karnxx/bonbon/images/Screenshot 2026-04-02 172829.png

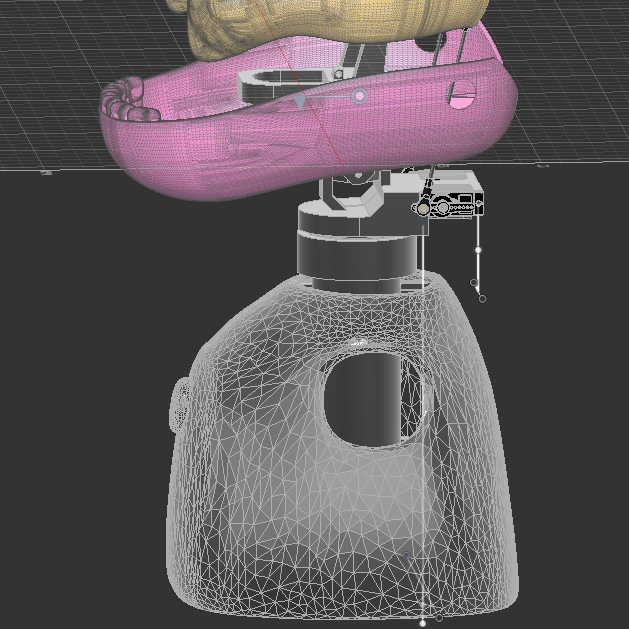
images/Screenshot 2026-04-02 172829.png
