karnxx/bonbon/cad/printed parts/stls/1xbothhands.stl

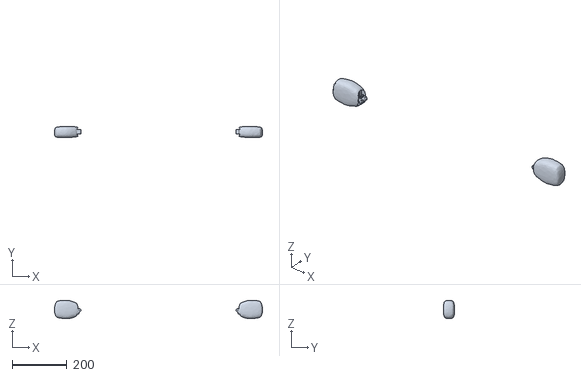
[picture p11: CAD file, 2026-04-18]
cad/printed parts/stls/1xbothhands.stl
756.6 x 40.9 x 67.3
