karnxx/bonbon/cad/printed parts/stls/1xuplidcontroller.stl

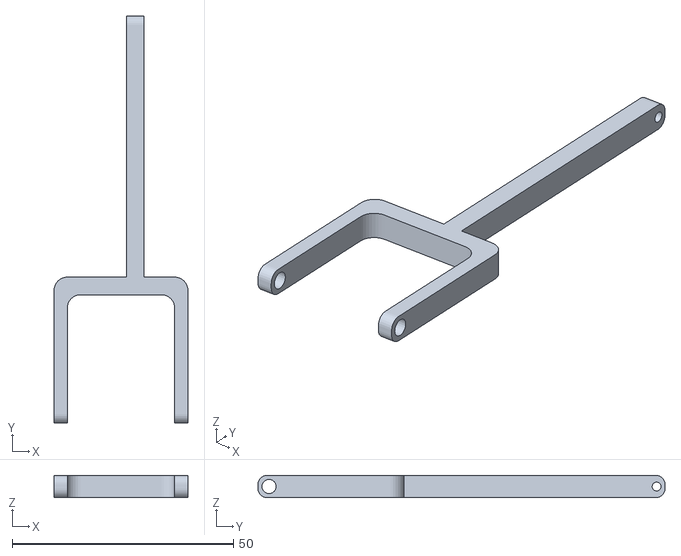
[picture p12: CAD file, 2026-04-18]
cad/printed parts/stls/1xuplidcontroller.stl
30.3 x 92.0 x 5.00
