karnxx/bonbon/cad/printed parts/stls/1xsnoutl.stl

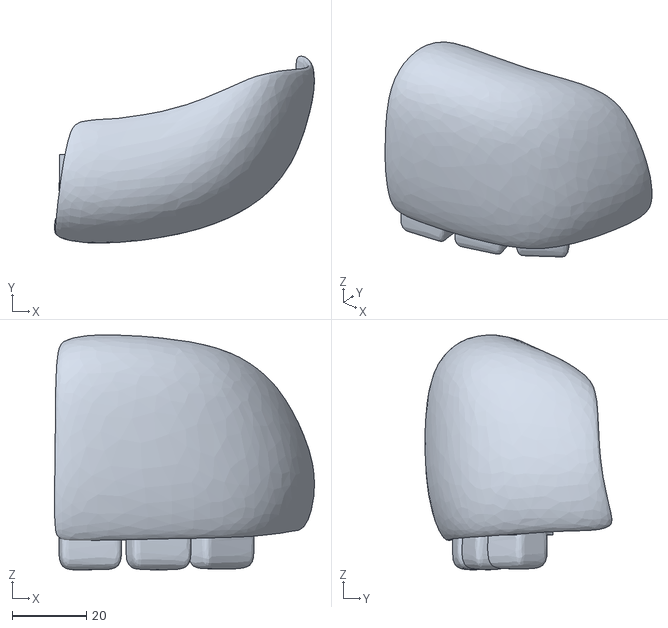
[picture p13: CAD file, 2026-04-18]
cad/printed parts/stls/1xsnoutl.stl
70.2 x 50.5 x 63.5
