karnxx/bonbon/cad/printed parts/stls/2xuptilt.stl

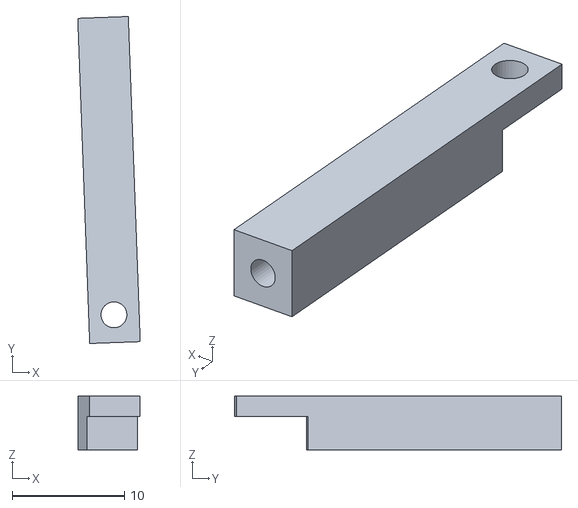
[picture p14: CAD file, 2026-04-18]
cad/printed parts/stls/2xuptilt.stl
5.56 x 29.1 x 4.80
