karnxx/bonbon/cad/printed parts/stls/1xjawshaft.stl

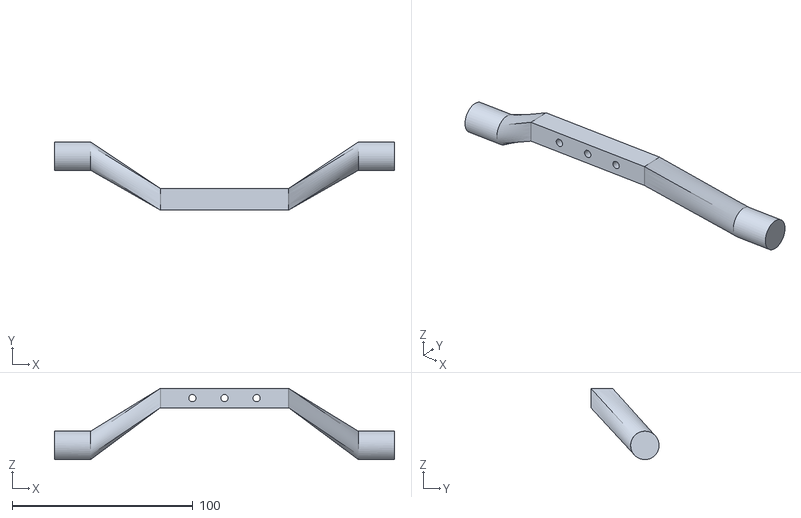
[picture p15: CAD file, 2026-04-18]
cad/printed parts/stls/1xjawshaft.stl
188.0 x 37.7 x 39.4
