karnxx/bonbon/cad/printed parts/stls/1xjaw.stl

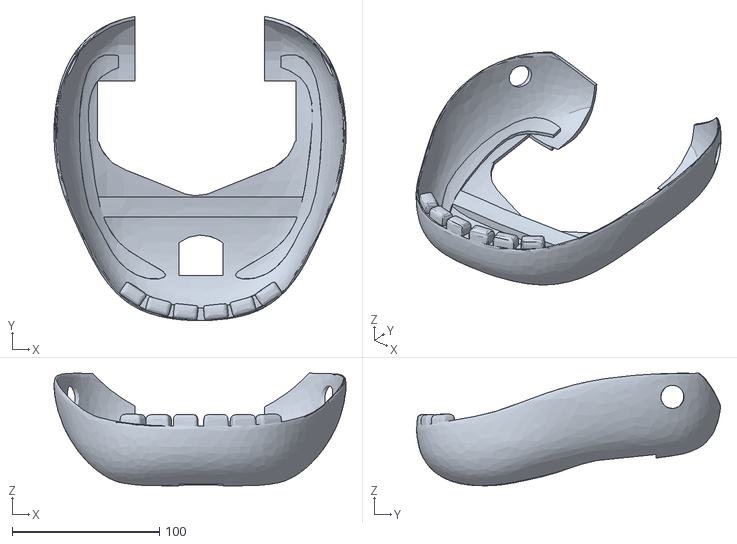
[picture p16: CAD file, 2026-04-18]
cad/printed parts/stls/1xjaw.stl
198.3 x 206.7 x 76.5
