karnxx/bonbon/cad/printed parts/stls/2xlowerear.stl

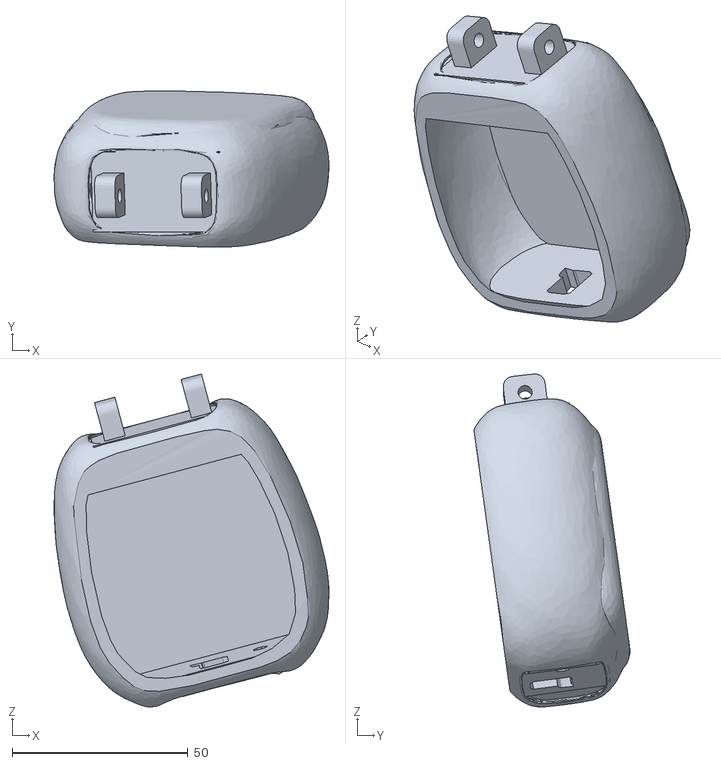
[picture p17: CAD file, 2026-04-18]
cad/printed parts/stls/2xlowerear.stl
78.2 x 44.4 x 94.8
