karnxx/bonbon/cad/printed parts/stls/1xskull.stl

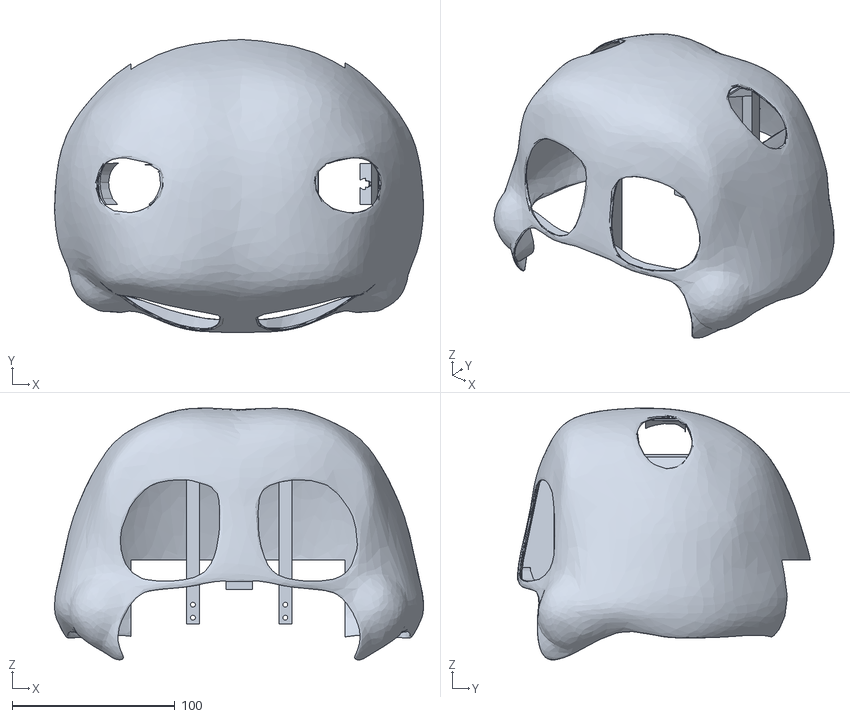
[picture p18: CAD file, 2026-04-18]
cad/printed parts/stls/1xskull.stl
227.0 x 180.2 x 155.0
