karnxx/bonbon/cad/printed parts/stls/1xdownlidcontroller.stl

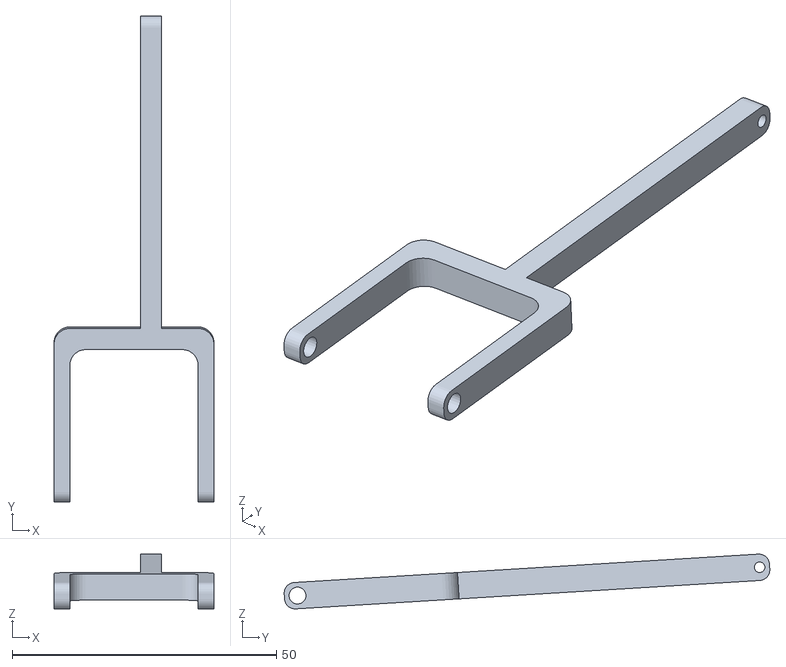
[picture p19: CAD file, 2026-04-18]
cad/printed parts/stls/1xdownlidcontroller.stl
30.3 x 91.9 x 10.4
