karnxx/bonbon/cad/printed parts/stls/1xuplid1.stl

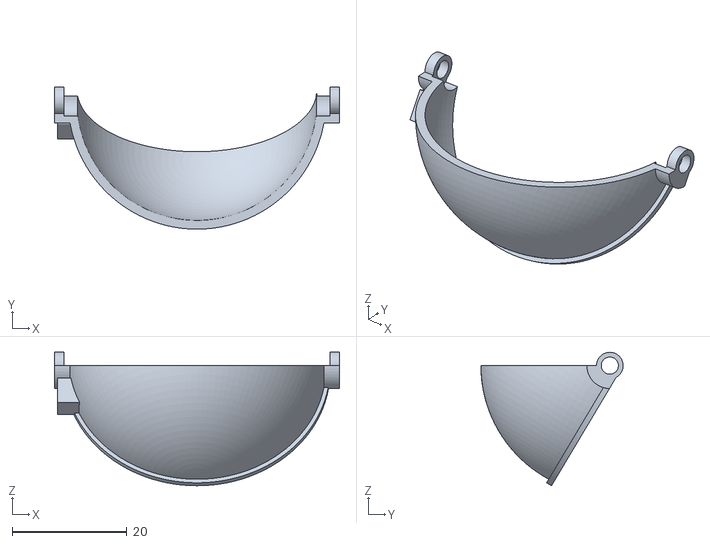
[picture p20: CAD file, 2026-04-18]
cad/printed parts/stls/1xuplid1.stl
49.7 x 24.8 x 23.3
