karnxx/bonbon/cad/printed parts/stls/2xuptiltpart.stl

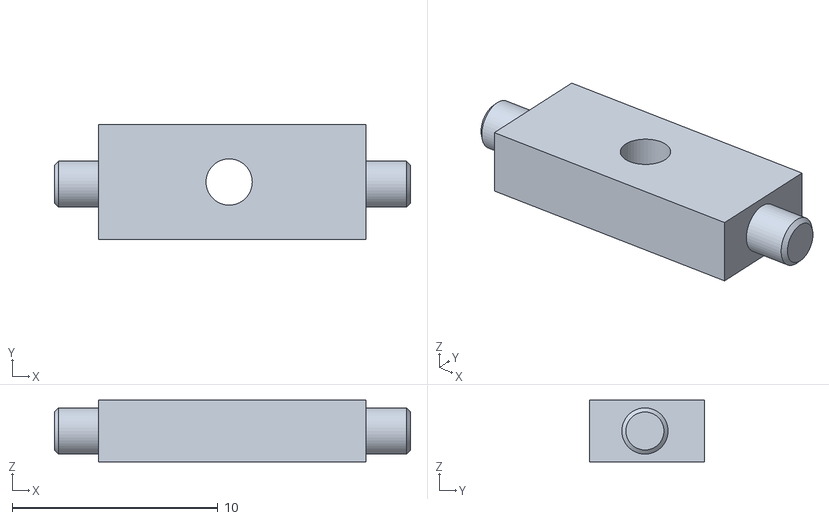
[picture p21: CAD file, 2026-04-18]
cad/printed parts/stls/2xuptiltpart.stl
17.3 x 5.60 x 3.00
