karnxx/bonbon/cad/printed parts/stls/2xeyeadapter.stl

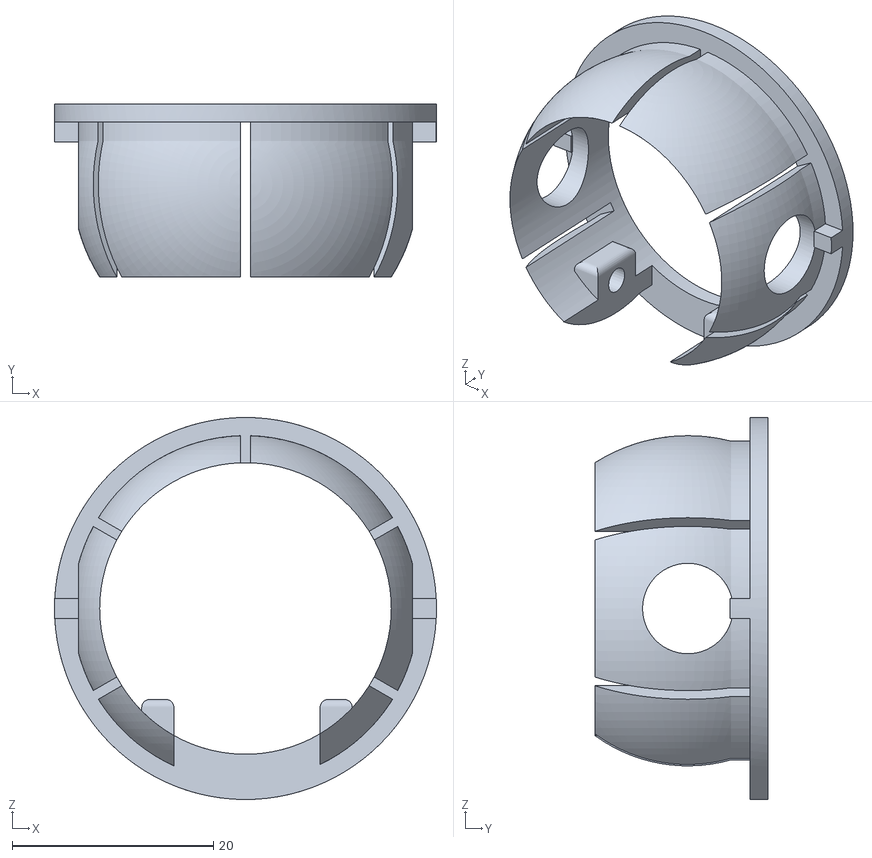
[picture p22: CAD file, 2026-04-18]
cad/printed parts/stls/2xeyeadapter.stl
38.0 x 17.3 x 38.0
