karnxx/bonbon/cad/printed parts/stls/2xearrod.stl

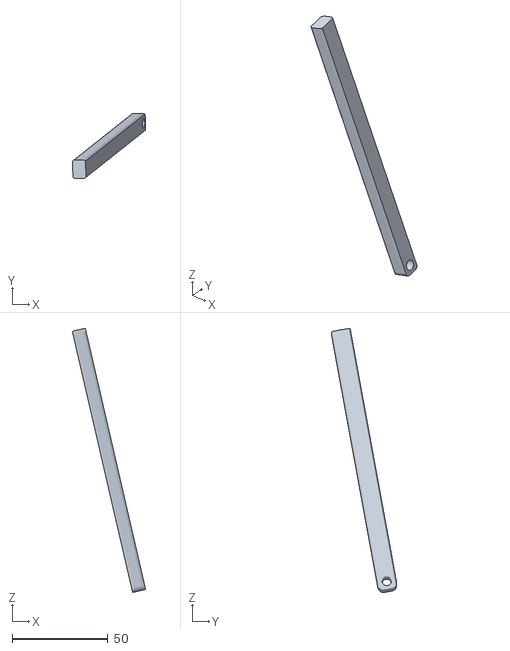
[picture p23: CAD file, 2026-04-18]
cad/printed parts/stls/2xearrod.stl
38.2 x 34.1 x 137.6
