karnxx/bonbon/cad/printed parts/stls/1xbothshoulders.stl

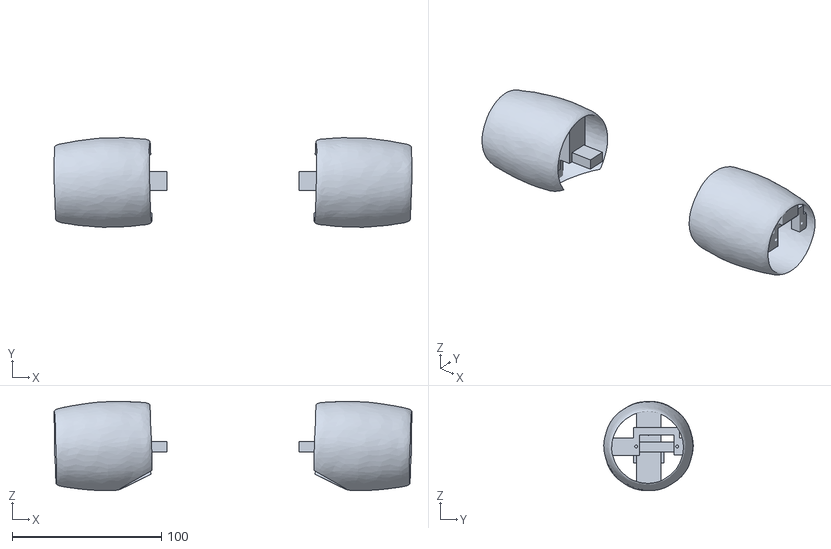
[picture p24: CAD file, 2026-04-18]
cad/printed parts/stls/1xbothshoulders.stl
239.9 x 60.1 x 59.7
