karnxx/bonbon/cad/printed parts/stls/2xcardaninner.stl

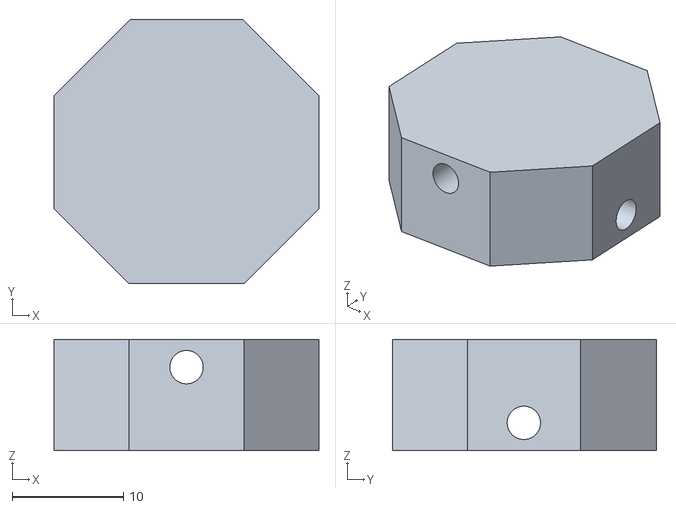
[picture p25: CAD file, 2026-04-18]
cad/printed parts/stls/2xcardaninner.stl
23.8 x 23.7 x 10.0
