karnxx/bonbon/cad/printed parts/stls/2xsidetiltforeye.stl

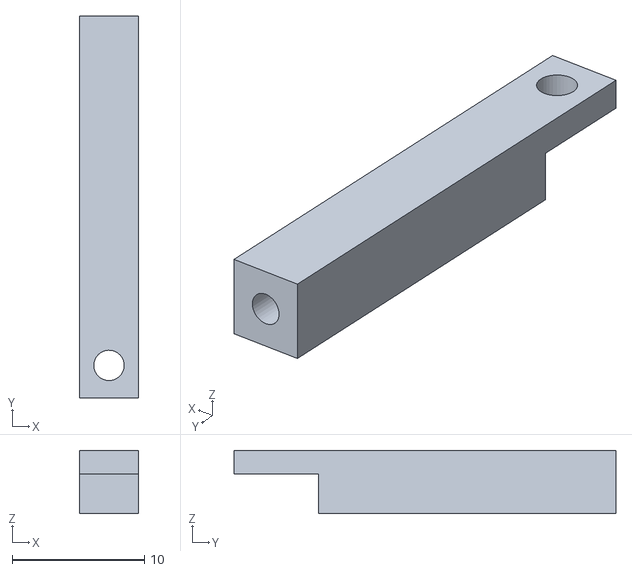
[picture p26: CAD file, 2026-04-18]
cad/printed parts/stls/2xsidetiltforeye.stl
4.50 x 28.9 x 4.80
