karnxx/bonbon/cad/printed parts/stls/2xuppearear.stl

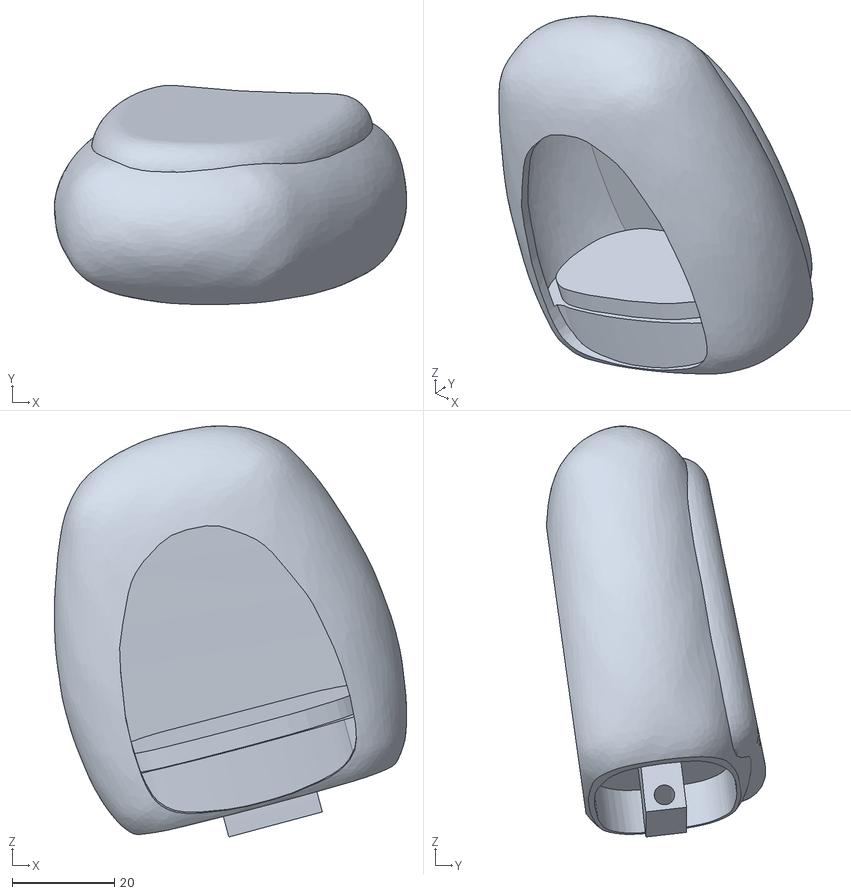
[picture p27: CAD file, 2026-04-18]
cad/printed parts/stls/2xuppearear.stl
68.8 x 42.8 x 80.2
