karnxx/bonbon/cad/printed parts/stls/1xtorso.stl

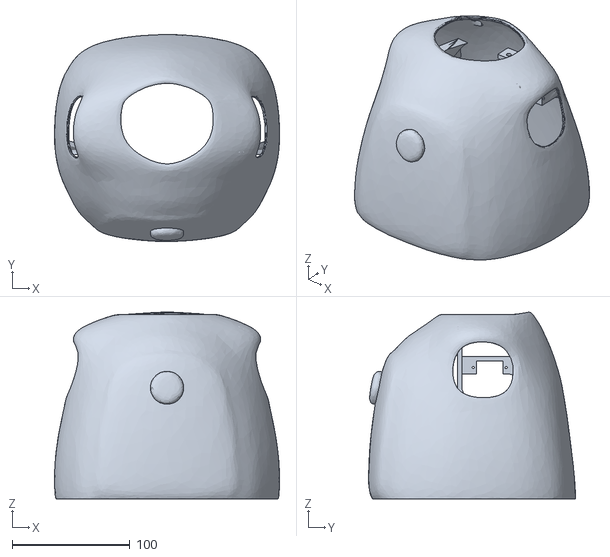
[picture p28: CAD file, 2026-04-18]
cad/printed parts/stls/1xtorso.stl
190.7 x 175.4 x 158.3
