karnxx/bonbon/cad/printed parts/stls/1xtorsogear.stl

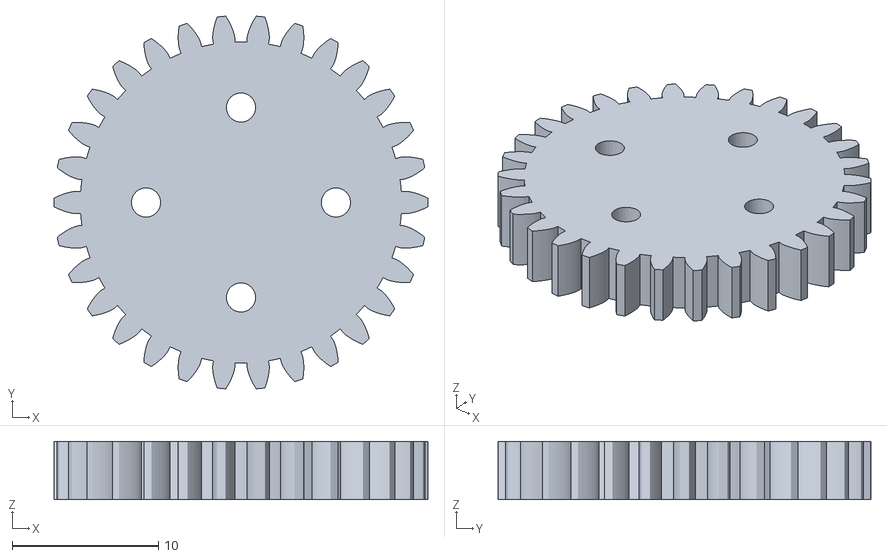
[picture p29: CAD file, 2026-04-18]
cad/printed parts/stls/1xtorsogear.stl
25.6 x 25.5 x 4.00
