karnxx/bonbon/cad/printed parts/stls/2xshoulderjoints.stl

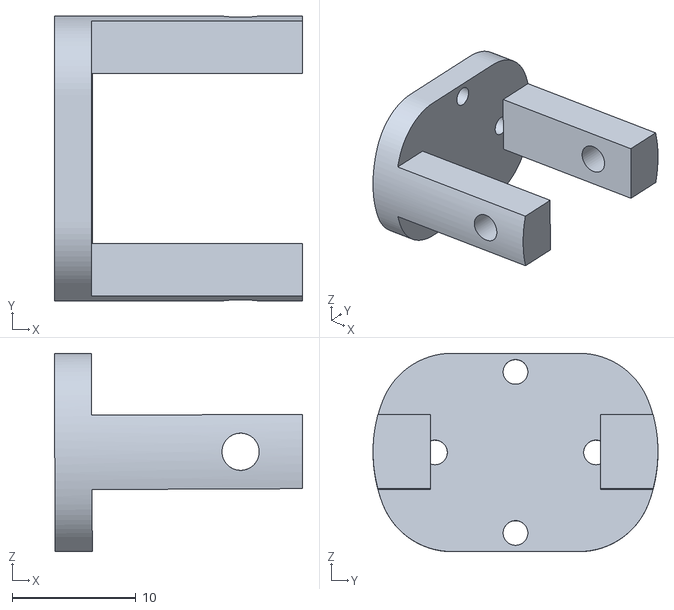
[picture p30: CAD file, 2026-04-18]
cad/printed parts/stls/2xshoulderjoints.stl
20.0 x 23.0 x 16.0
