karnxx/bonbon/cad/printed parts/stls/2xmiddlerotationpart.stl

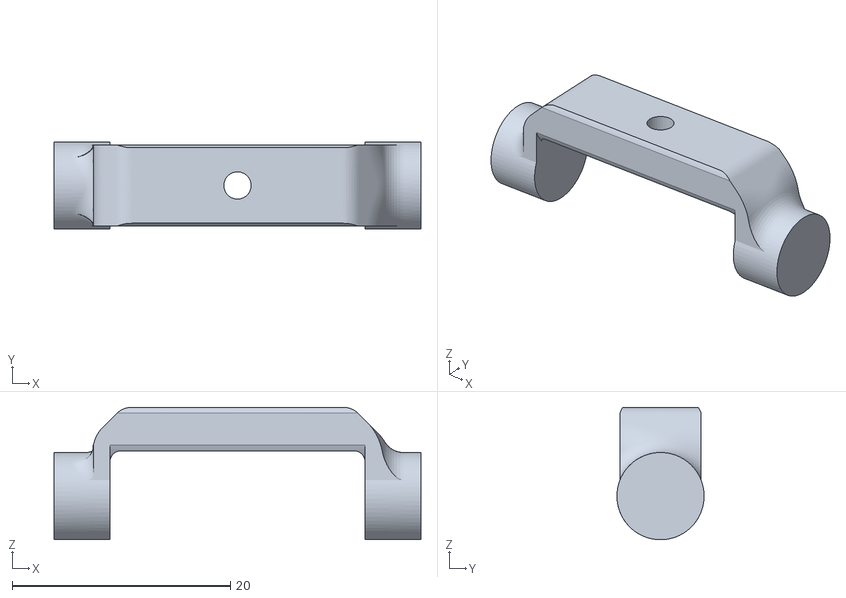
[picture p31: CAD file, 2026-04-18]
cad/printed parts/stls/2xmiddlerotationpart.stl
33.7 x 8.00 x 12.1
